nistordarius26h-ship-it/esp32s3-brucey/media/IMG_20260915_202625.jpg

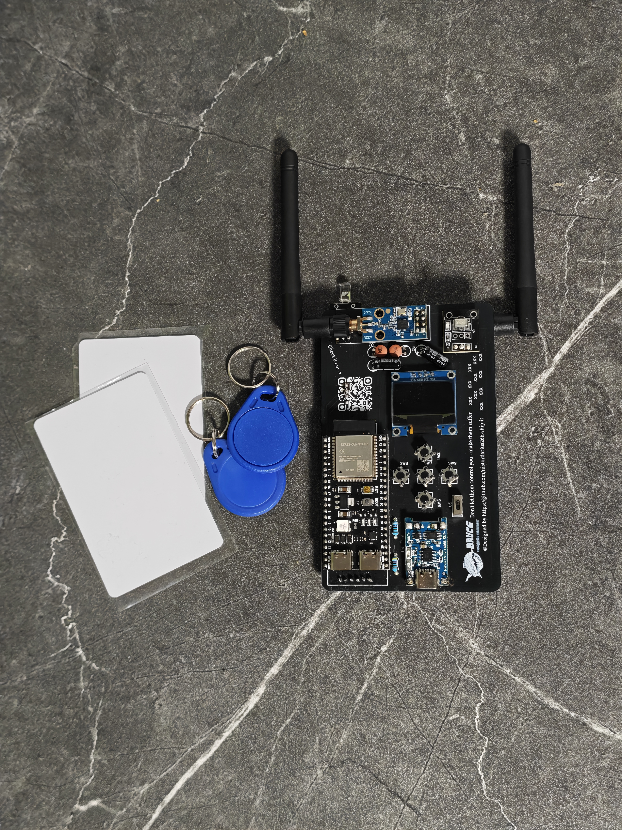
media/IMG_20260915_202625.jpg
